kushima8/PMW3360/stl/reex_34mm_low.stl

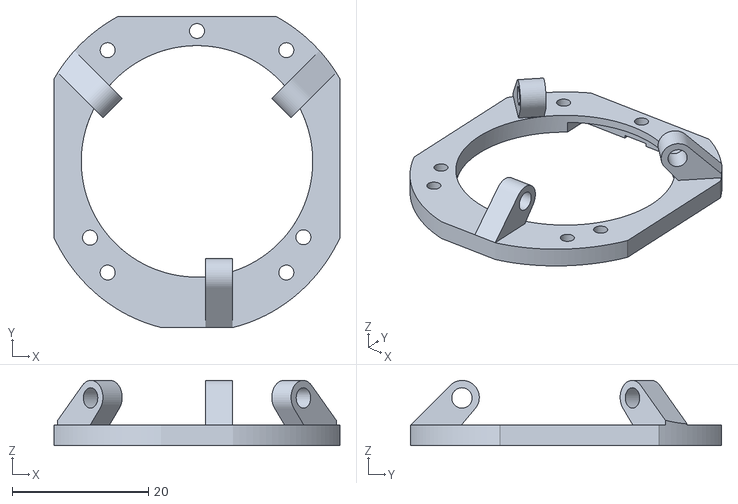
[picture p15: CAD file, 2024-11-24, an earlier design]
stl/reex_34mm_low.stl
42.0 x 45.7 x 9.57
